rupnikk/LED_okrasek/Software/LED_okrasek/Source/led_okrasek.h

/*
 * led_okrasek.h
 *
 *  Created on: 10. jan. 2017
 *      Author: urban
 */

#ifndef SOURCE_LED_OKRASEK_H_
#define SOURCE_LED_OKRASEK_H_

#include <avr/io.h>
#include <avr/interrupt.h>
#include <avr/pgmspace.h>
#include <util/delay.h>
#include "stdint.h"
#include "stdlib.h"
#include "bittop.h"
#include "hardware.h"
#include "timer.h"
#include "pwm.h"
#include "blink.h"
#include "note.h"
#include "int.h"
#include "pesmi.h"


#endif /* SOURCE_LED_OKRASEK_H_ */
