rupnikk/LED_okrasek/Software/LED_okrasek/Source/int.h

/*
 * int.h
 *
 *  Created on: 3. jan. 2017
 *      Author: Urban Rupnik
 *      City: Zadlog 42
 */

#ifndef SOURCE_INT_H_
#define SOURCE_INT_H_


/*******************************
 ***KONFIGURACIJSKE FUNKCIJE****
 *******************************/
void IntCfg();


/*******************************
 ************FUNKCIJE***********
 *******************************/
void pcint_en(uint8_t x);
void pcint_dis(uint32_t x);

#endif /* SOURCE_INT_H_ */
